FromDarkHell/LegoDimensionsRGB/research/PS3-Playpad/Photos/PXL_20250806_044009409.png

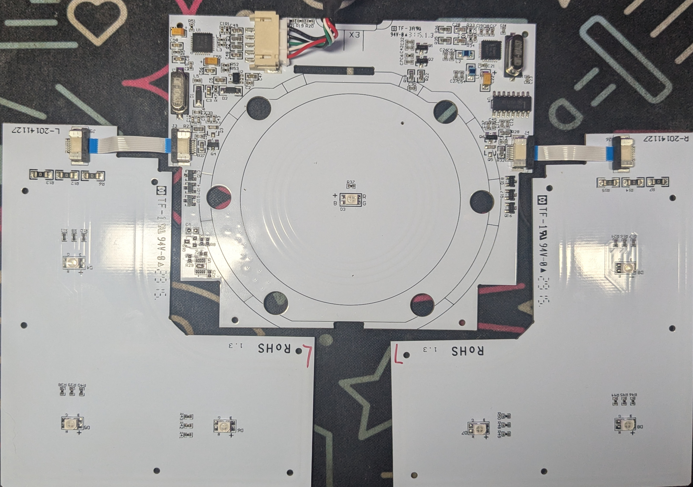
research/PS3-Playpad/Photos/PXL_20250806_044009409.png
