FromDarkHell/LegoDimensionsRGB/projects/basic-emulator/firmware/include/lego/hid/constants.h

#pragma once

#include <Arduino.h>

constexpr int PLAYPAD_MAX_PACKET_SIZE = 0x0020;
constexpr int NUM_PADS = 0x03;

/**
 * @brief PS3 / PC playpad (original PDP reader).
 *  VID 0x0E6F  PID 0x0241  "LEGO READER V2.10"
 *  Packets have a standard [type][length][cmd_type]... layout.
 */
#define PS3_PLAYPAD_VENDOR_ID 0x0E6F
#define PS3_PLAYPAD_PRODUCT_ID 0x0241
#define PS3_PLAYPAD_PRODUCT "LEGO READER V2.10"
#define PS3_PLAYPAD_MANUFACTURER "PDP LIMITED. "
#define PS3_PLAYPAD_SERIAL "P.D.P.000000"
#define PS3_PLAYPAD_VERSION 0x0100

#define X360_PLAYPAD_VENDOR_ID 0x24C6
#define X360_PLAYPAD_PRODUCT_ID 0xFA01
#define X360_PLAYPAD_PRODUCT "LEGO(R) DIMENSIONS(TM)"
#define X360_PLAYPAD_MANUFACTURER "Warner Bros."

#define X360_PLAYPAD_SERIAL "03108E28"
#define X360_PLAYPAD_VERSION 0x0100

/**
 * @brief Selects which console/platform the emulator presents itself as.
 *
 *  The value is persisted in the Config store under the key "platform"
 *  and can be changed via the web UI (or via the hardware-level switch).
 *
 *  PS3 has basic packets (see other files)
 *  X360 adds in an extra packet prefix, plus requires XSM3 authentication on retail consoles, and
 * has different VID/PIDs
 */
enum class ToypadPlatform : uint8_t {
    PS3 = 0x00,
    X360 = 0x01,
};

/**
 * @brief A byte enum defining whether or not a packet is a command (aka sent by the game -> pad
 * *or* an "event" which is pad -> game)
 *
 */
enum class PacketType : uint8_t {
    COMMAND = 0x55,
    EVENT = 0x56,
};

/**
 * @brief An enum which describes all of the command types
 *
 */
enum class GatewayCommand : uint8_t {
    // A WAKE packet is used to start the handshaking process with a playpad
    WAKE = 0xB0,
    // A SEED packet is the next step in the handshaking process, and involves setting the PRNG to
    // the correct seed
    SEED = 0xB1,
    // A CHALLENGE packet is the 3rd & final step and involves checking if the PRNG implementation
    // is correct, in addition to the encryption.
    CHALLENGE = 0xB3,

    // Sets the current color of the specifically indexed pad
    COL = 0xC0,
    // Gets the current color of the specific pad
    GETCOL = 0xC1,
    // Fades the specific pad to a specific color over x amount of ticks and cycles it y amount of
    // times
    FADE = 0xC2,
    // Flashes the specific pad back and forth from a specific color over x amount of ticks and
    // cycles it y amount of times
    FLASH = 0xC3,

    FADRD = 0xC4,  // TODO: Needs implemented

    // Fades all pads in a single command to a specific color over x amount of ticks and cycles it y
    // amount of times
    FADAL = 0xC6,
    // Flashes all pads in a single command to a specific color over x amount of ticks and cycles it
    // y amount of times

    FLSAL = 0xC7,
    // Colors all pads in a single command to a specific color

    COLAL = 0xC8,

    // Returns an array of bitfields of all of the current tag locations and their indexes
    TGLST = 0xD0,

    // Reads NFC data from the NFCTag
    READ = 0xD2,
    // Writes NFC data onto the NFC tag
    WRITE = 0xD3,
    // The MODEL command gets extra info (IDs) from the specific NFC tag at a given index
    MODEL = 0xD4,

    // The playpad itself automatically sets/changes the PWD for a given NFC tag.
    // This command lets you turn on/off the PWD.
    // See: https://github.com/AlinaNova21/node-ld/blob/master/src/lib/ToyPad.js
    PWD = 0xE1,

    // This command lets you turn on/off all NFC operations until another read/write/active command
    // is called
    ACTIVE = 0xE5,  // TODO: Needs implemented

    // ???
    LEDSEQ = 0xFF,
};

/**
 * @brief A struct for defining R/G/B colors for a specific pad
 *
 */
struct PadColor {
    uint8_t r, g, b;

    /**
     * @brief Returns a pad color based on a 3-byte long buffer
     *
     * @param hex The buffer to read 3 bytes off of and then convert to a color
     * @return PadColor A pad color from the first 3 bytes of the buffer
     */
    static inline PadColor fromBuffer(const uint8_t* hex) { return {hex[0], hex[1], hex[2]}; }

    /**
     * @brief Converts a PadColor to a uint32 like 0xFF00FF
     *
     * @return uint32_t
     */
    inline uint32_t toHex() { return ((r & 0xff) << 16) + ((g & 0xff) << 8) + (b & 0xff); }

    /**
     * @brief Linearly interpolates a color from `a` -> `b` at percentage `t`
     *
     * @param a The starting color
     * @param b The ending color
     * @param t A percentage to interpolate
     * @return PadColor The interpolated color at `t`% between `a` and `b`
     */
    static PadColor lerpColor(const PadColor& a, const PadColor& b, float t) {
        return {
            (uint8_t)(a.r + (int16_t)(b.r - a.r) * t),
            (uint8_t)(a.g + (int16_t)(b.g - a.g) * t),
            (uint8_t)(a.b + (int16_t)(b.b - a.b) * t),
        };
    }

    static constexpr PadColor Black() { return {0x00, 0x00, 0x00}; }
    static constexpr PadColor White() { return {0xFF, 0xFF, 0xFF}; }
    static constexpr PadColor Red() { return {0xFF, 0x00, 0x00}; }
    static constexpr PadColor Green() { return {0x00, 0xFF, 0x00}; }
    static constexpr PadColor Blue() { return {0x00, 0x00, 0xFF}; }

    bool operator==(const PadColor& o) const { return r == o.r && g == o.g && b == o.b; }
    bool operator!=(const PadColor& o) const { return !(*this == o); }
};

/**
 * @brief An enum detailing all of the locations/values for the specific playpad colors/etc.
 *
 */
enum class PadLocation : uint8_t {
    ALL = 0x00,

    CENTER = 0x01,
    LEFT = 0x02,
    RIGHT = 0x03
};
